krebsd/current-diffamp/layout/pdf/DiffAmp-F.SilkS.pdf

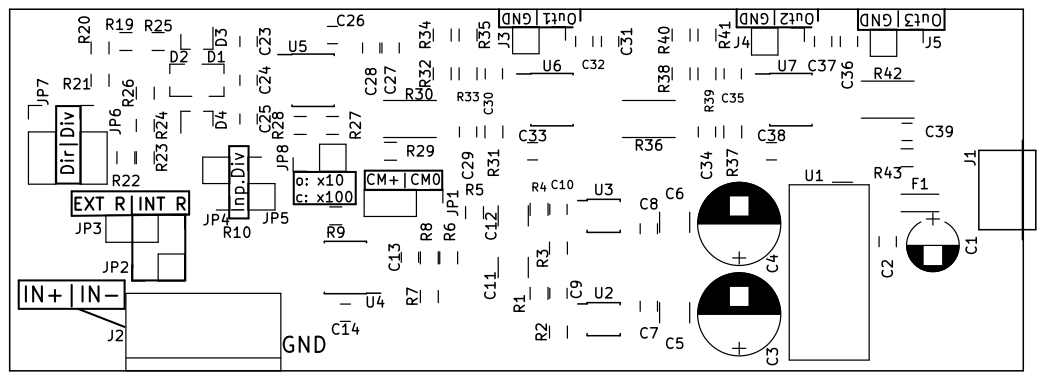
[picture p14: page 1]
